jiangotto/Pomo/Assets/TestPatterns/epd_16_grayscale_1216x684.png

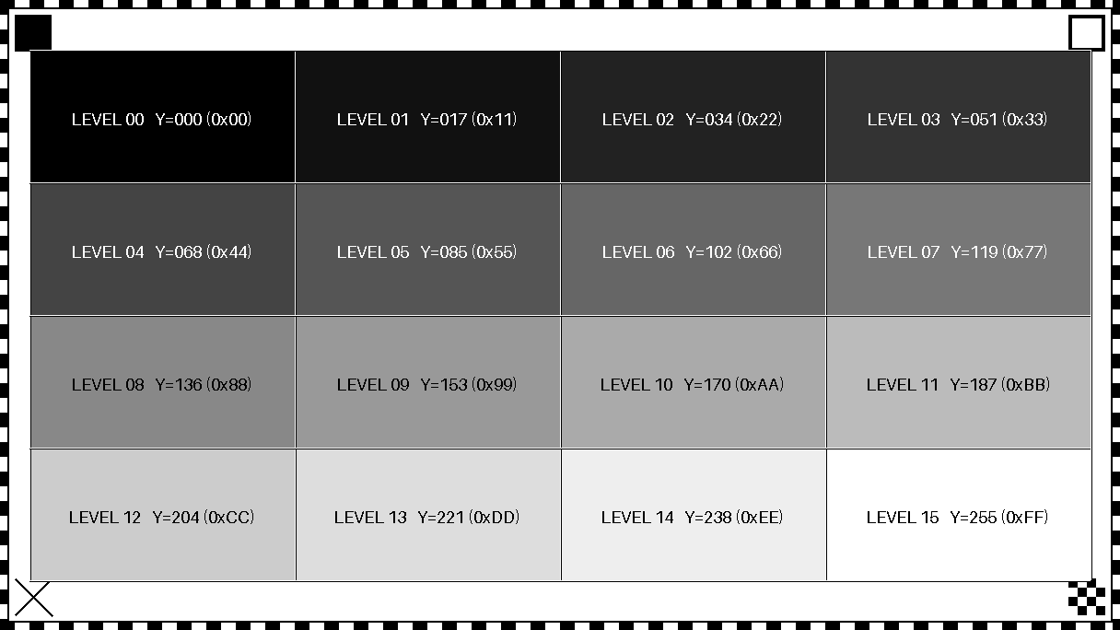
Assets/TestPatterns/epd_16_grayscale_1216x684.png
