jiangotto/Pomo/Firmware/V2/src/pomo.v

// Copyright Yuhan Jiang 2025-2026
//
// This source describes Open Hardware and is licensed under the CERN-OHL-S v2
//
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
`timescale 1ns/1ps
`include "defines.vh"

module pomo (
	input  wire         clk,
	input  wire         sys_ready,
	input  wire         rst,

	input  wire         vin_vsync,
	input  wire         vin_hsync,
	input  wire         vin_de,
	input  wire [3:0]   vin_pixel,
	input  wire         mode_cmd_valid,
	input  wire [3:0]   mode_cmd_value,
	input  wire         reinit_cmd_valid,

	output wire         bo_clk,
	output wire         bo_vsync,
	output wire         bo_de,
	output reg  [15:0]  bo_data,
	output wire         bi_clk,
	output wire         bi_vsync,
	output wire         bi_de,
	input  wire         bi_den,
	input  wire [15:0]  bi_data,
	output reg  [3:0]   active_mode,

	output wire         epd_gdclk,
	output wire         epd_gdsp,
	output wire         epd_sdclk,
	output wire         epd_sdle,
	output wire [15:0]  epd_data,
	output wire         epd_sdce
);
	// sys_ready combines PMIC state from sys_clk with HyperRAM calibration
	// state from the memory domain.  Synchronize the resulting stable level
	// before it controls any state in this pixel-clock domain.
	(* ASYNC_REG = "TRUE", syn_preserve = 1 *) reg [1:0] sys_ready_sync;
	always @(posedge clk) begin
		if (rst)
			sys_ready_sync <= 2'b00;
		else
			sys_ready_sync <= {sys_ready_sync[0], sys_ready};
	end
	wire sys_ready_clk = sys_ready_sync[1];

	// ============================================================
	// Scan Control
	//
	// Vertical:   counter-based. Frame line counts match defines.
	// Horizontal: signal-based. MIPI actual hsync/de timing may differ.
	// ============================================================

	// vertical timing (from defines, frame line counts are reliable)
	localparam [7:0]  VFP   = `DEFAULT_VFP;
	localparam [7:0]  VSYNC = `DEFAULT_VSYNC;
	localparam [7:0]  VBP   = `DEFAULT_VBP;
	localparam [11:0] VACT  = `EPD_VACT;

	// input edge detect
	reg vin_vsync_d;
	reg vin_hsync_d;

	always @(posedge clk) begin
		if (rst) begin
			vin_vsync_d <= 1'b0;
			vin_hsync_d <= 1'b0;
		end else begin
			vin_vsync_d <= vin_vsync;
			vin_hsync_d <= vin_hsync;
		end
	end

	wire vin_vsync_rise = vin_vsync & ~vin_vsync_d;
	wire vin_hsync_rise = vin_hsync & ~vin_hsync_d;

	// frame_valid: high from first hsync after vsync to last line of frame
	// vertical line counter
	reg        frame_valid;
	reg        frame_first_line;
	reg        vsync_just_hit;
	reg [10:0] scan_v_cnt;
	reg [5:0]  al_framecnt;

	always @(posedge clk) begin
		if (rst) begin
			frame_valid      <= 1'b0;
			frame_first_line <= 1'b0;
			vsync_just_hit   <= 1'b0;
			scan_v_cnt       <= 11'd0;
			al_framecnt      <= `LUT_FRAMES;
		end else if (!sys_ready_clk) begin
			frame_valid      <= 1'b0;
			frame_first_line <= 1'b0;
			vsync_just_hit   <= 1'b0;
			scan_v_cnt       <= 11'd0;
			al_framecnt      <= `LUT_FRAMES;
		end else begin
			vsync_just_hit <= vin_vsync_rise;

			if (vin_vsync_rise) begin
				frame_valid      <= 1'b0;
				frame_first_line <= 1'b1;
				scan_v_cnt       <= 11'd0;
				if (al_framecnt == 6'd0)
					al_framecnt <= `LUT_FRAMES;
				else
					al_framecnt <= al_framecnt - 6'd1;
			end else if ((frame_first_line && vin_hsync_rise) || (vsync_just_hit && vin_hsync)) begin
				frame_valid      <= sys_ready_clk;
				frame_first_line <= 1'b0;
				scan_v_cnt       <= 11'd0;
			end else if (frame_valid && vin_hsync_rise) begin
				frame_first_line <= 1'b0;
				if (scan_v_cnt == (VFP + VSYNC + VBP + VACT - 1'b1)) begin
					scan_v_cnt  <= 11'd0;
					frame_valid <= 1'b0;
				end else begin
					scan_v_cnt <= scan_v_cnt + 11'd1;
				end
			end else if (frame_valid) begin
				frame_first_line <= 1'b0;
			end else begin
				scan_v_cnt       <= 11'd0;
				frame_valid      <= 1'b0;
				frame_first_line <= 1'b0;
			end
		end
	end

	// scan region signals
	// vertical: counter-based
	// horizontal: signal-based (vin_hsync, vin_de)
	wire scan_in_vsync;
	wire scan_in_vbp;
	wire scan_in_vact;
	wire scan_in_vact_le;
	wire scan_in_gate_start;
	wire scan_in_gate_blank;
	wire scan_in_hsync;
	wire scan_in_hact;
	wire scan_in_act;

	assign scan_in_vsync = vin_vsync;
	assign scan_in_vbp   = frame_valid && (scan_v_cnt >= VSYNC) && (scan_v_cnt < VSYNC + VBP);
	assign scan_in_vact  = frame_valid && (scan_v_cnt >= VSYNC + VBP) && (scan_v_cnt < VSYNC + VBP + VACT);
	// Pomo streams a completed Source row into the panel one line before it is
	// latched.  Keep the established next-line window; Caster obtains the same
	// relationship from the phase of its own free-running scan counter.
	assign scan_in_vact_le = frame_valid &&
		(scan_v_cnt >= VSYNC + VBP + 1) &&
		(scan_v_cnt < VSYNC + VBP + VACT + 1);
	// Start STV early enough that the first active line supplies the final
	// internal shift before G1. Keep clocking through the trailing VFP so the
	// last Source row, latched there, receives the final Gate selection.
	localparam [10:0] GATE_START_LINE = VSYNC + VBP -
		(`EPD_STV_TO_G1_CKV - 1);
	assign scan_in_gate_start = frame_valid &&
		(scan_v_cnt == GATE_START_LINE);
	assign scan_in_gate_blank = frame_valid &&
		(scan_v_cnt >= GATE_START_LINE) && !scan_in_vact;
	assign scan_in_hsync = frame_valid && vin_hsync;
	assign scan_in_hact  = frame_valid && vin_de;
	assign scan_in_act   = scan_in_vact && scan_in_hact;

	reg after_hact;
	always @(posedge clk) begin
		if (rst)
			after_hact <= 1'b0;
		else if (vin_de)         
			after_hact <= 1'b1;  
		else if (vin_hsync)      
			after_hact <= 1'b0; 
	end
	wire scan_in_hbp = frame_valid && !vin_hsync && !vin_de && !after_hact;
	wire scan_in_hfp = frame_valid && !vin_hsync && !vin_de &&  after_hact;

	// ============================================================
	// Blue noise coordinates
	// ============================================================
	// Count the physical source coordinate at the reordered stream. The blue
	// noise ROM is 64x64, so both coordinates must retain six address bits.
	reg [5:0] noise_phys_x;

	always @(posedge clk) begin
		if (rst)
			noise_phys_x <= 6'd0;
		else if (vin_hsync_rise)
			noise_phys_x <= 6'd0;
		else if (vin_de)
			noise_phys_x <= noise_phys_x + 6'd1;
	end

	// Remove the vertical blanking offset before addressing the noise tile.
	// In reorder mode, convert the physical W x 2H scan coordinate back to
	// the original logical 2W x H coordinate so adjacent logical pixels use
	// adjacent entries of the blue-noise pattern:
	//   logical_x = 2*physical_x + physical_y[0]
	//   logical_y = physical_y / 2
	wire [10:0] noise_phys_y = scan_v_cnt - (VSYNC + VBP);
`ifdef EPD_PIXEL_REORDER
	wire [5:0] noise_x = {noise_phys_x[4:0], noise_phys_y[0]};
	wire [5:0] noise_y = noise_phys_y[6:1];
`else
	wire [5:0] noise_x = noise_phys_x;
	wire [5:0] noise_y = noise_phys_y[5:0];
`endif

	// ============================================================
	// Auto clear timer
	// ============================================================



	// ============================================================
	// Init state machine
	// ============================================================

	localparam INIT_IDLE     = 2'd0;
	localparam INIT_CLEARING = 2'd1;
	localparam INIT_NORMAL   = 2'd2;

	reg [1:0] init_state;
	reg [9:0] clear_frame_cnt;
	reg [3:0] requested_mode;

	function is_display_mode;
		input [3:0] mode;
		begin
			is_display_mode = (mode == 4'h8) || (mode == 4'hA) ||
			                  (mode == 4'hB) || (mode == 4'hC);
		end
	endfunction

	always @(posedge clk) begin
		if (rst) begin
			init_state      <= INIT_IDLE;
			clear_frame_cnt <= 10'd0;
			requested_mode  <= `EPD_DEFAULT_MODE;
			active_mode     <= `EPD_DEFAULT_MODE;
		end else begin
			if (mode_cmd_valid && is_display_mode(mode_cmd_value))
				requested_mode <= mode_cmd_value;

			if (!sys_ready_clk) begin
				// A PMIC power cycle always restarts the normal clear sequence.
				init_state      <= INIT_IDLE;
				clear_frame_cnt <= 10'd0;
			end else if (reinit_cmd_valid) begin
				// Preserve requested_mode, but restart the complete initialization
				// clear at the next clean input-frame boundary.
				init_state      <= INIT_IDLE;
				clear_frame_cnt <= 10'd0;
			end else case (init_state)
				INIT_IDLE: begin
					if (sys_ready_clk && vin_vsync_rise) begin
						active_mode <= requested_mode;
						init_state <= INIT_CLEARING;
					end
				end
				INIT_CLEARING: begin
					if (vin_vsync_rise) begin
						if (requested_mode != active_mode) begin
							active_mode <= requested_mode;
							clear_frame_cnt <= 10'd0;
						end else if (clear_frame_cnt == `CLEAR_FRAMES) begin
							init_state <= INIT_NORMAL;
							clear_frame_cnt <= 10'd0;
						end else begin
							clear_frame_cnt <= clear_frame_cnt + 10'd1;
						end
					end
				end
				INIT_NORMAL: begin
					if (vin_vsync_rise && (requested_mode != active_mode)) begin
						active_mode <= requested_mode;
						init_state <= INIT_CLEARING;
						clear_frame_cnt <= 10'd0;
					end
				end
			endcase
		end
	end

	wire [1:0] sys_mode;
	assign sys_mode = (init_state == INIT_CLEARING) ? `SYS_CLEAR : `SYS_NORMAL;

	// ============================================================
	// BI & BO
	// ============================================================

	assign bi_clk   = clk;
	assign bi_vsync = ~scan_in_vsync;
	assign bi_de    = scan_in_act;

	wire bi_vsync_dl;
	delay #(
		.DEPTH(6), 
		.WIDTH(1)
	) u_delay_bi_vsync (
		.clk(clk), 
		.rst(rst),
		.din(bi_vsync),
		.dout(bi_vsync_dl)
	);

	wire bi_de_dl;
	delay #(
		.DEPTH(6), 
		.WIDTH(1)
	) u_delay_bi_de (
		.clk(clk), 
		.rst(rst),
		.din(bi_de),
		.dout(bi_de_dl)
	);

	assign bo_clk   = clk;
	assign bo_vsync = bi_vsync_dl;
	assign bo_de    = bi_de_dl;

	// ============================================================
	// Stage 1 — 2-cycle delay, align vin_pixel with HyperRAM read
	// ============================================================

//  wire s1_active;
//  delay #(
//      .DEPTH(2), 
//      .WIDTH(1)
//  ) u_delay_s1_active (
//      .clk(clk), 
//      .rst(rst),
//      .din(bi_de),
//      .dout(s1_active)
//  );

	wire [3:0] s1_vin_pixel;
	delay #(
		.DEPTH(2), 
		.WIDTH(4)
	) u_delay_s1p (
		.clk(clk), 
		.rst(rst),
		.din(vin_pixel),
		.dout(s1_vin_pixel)
	);

	// ============================================================
	// Stage 2 — latch framebuffer read + aligned input pixel
	// ============================================================
	reg        s2_active;
	reg [15:0] s2_bi_pixel;
	reg [3:0]  s2_vin_pixel;

	always @(posedge clk) begin
		if (rst) begin
			s2_active <= 1'b0;
		end else begin
			s2_active <= bi_den;
			if (bi_den) begin
				s2_bi_pixel  <= bi_data;
				s2_vin_pixel <= s1_vin_pixel;
			end
		end
	end

		// ============================================================
		// Blue noise dithering
		// ============================================================
		wire [7:0] s2_vin_linear = {s2_vin_pixel, 4'b0};
		wire       s3_dith_1b;
		wire [3:0] s3_dith_4b;

		blue_noise_dithering u_dith (
			.clk     (clk),
			.rst     (rst),
			.vin     (s2_vin_linear),
			.vout_1b (s3_dith_1b),
			.vout_4b (s3_dith_4b),
			.x_pos   (noise_x),
			.y_pos   (noise_y)
		);

	// ============================================================
	// Stage 3 — LUT address generation & wvfmlut
	// ============================================================

	reg        s3_active;
	reg [15:0] s3_bi_pixel;
	reg [3:0]  s3_vin_pixel;

	always @(posedge clk) begin
		if (rst) begin
			s3_active <= 1'b0;
		end else begin
			s3_active    <= s2_active;
			s3_bi_pixel  <= s2_bi_pixel;
			s3_vin_pixel <= s2_vin_pixel;
		end
	end

	// Waveform lookup here
	// Waveform structure:
	// 14 bit address input
	//   6 bit sequence ID
	//   4 bit source grayscale
	//   4 bit destination grayscale
	// 2 bit data output
	// 32 Kb
	wire [13:0] ram_addr_rd;
	wire [1:0]  s4_lut_rd; // 1 cycle latency

	// See pixel_processing.v comments for more details
	// Only used for LUT modes.
	// Local counter (per pixel counter) is used for manual LUT modes
	// Global counter is used for auto LUT modes
	/*verilator lint_off UNUSEDSIGNAL */
	wire [15:0] wvfm_bi = s3_bi_pixel;
	/*verilator lint_on UNUSEDSIGNAL */
	wire use_local_counter =  wvfm_bi[15];
	wire [5:0] wvfm_fcnt_global_counter = wvfm_bi[9:4];
	wire [5:0] wvfm_fcnt_local_counter = al_framecnt;
	wire [5:0] wvfm_fcnt = use_local_counter ?
			wvfm_fcnt_local_counter : wvfm_fcnt_global_counter;
	wire [5:0] wvfm_fseq = `LUT_FRAMES - wvfm_fcnt;
	wire [3:0] wvfm_src_global_counter = wvfm_bi[13:10];
	wire [3:0] wvfm_src_local_counter = wvfm_bi[7:4];
	wire [3:0] wvfm_src = use_local_counter ?
			wvfm_src_local_counter : wvfm_src_global_counter;
	wire [3:0] wvfm_tgt = wvfm_bi[3:0];
	assign ram_addr_rd = {wvfm_fseq, wvfm_tgt, wvfm_src};

	wvfmlut u_wcfmlut (
		.clk    (clk),
		.rst    (rst),
		.en     (s3_active),
		.addr   (ram_addr_rd),
		.dout   (s4_lut_rd)
	);

	// ============================================================
	// Stage 4 — pixel_processing 
	// ============================================================

	reg        s4_active;
	reg [15:0] s4_bi_pixel;
	reg [3:0]  s4_vin_pixel;
	reg [3:0]  s4_proc_vin;

	// Select the dithered value before the Stage 4 register boundary.  The
	// original pixel is retained separately because Auto-LUT also needs the
	// undithered input.  This moves the mode/dither mux out of the long pixel
	// state-machine path without adding a pipeline cycle.
	wire [3:0] s3_pixel_mode = s3_bi_pixel[15:12];
	wire       s3_use_dither_1b = (s3_pixel_mode == 4'hA);
	wire       s3_use_dither_4b =
		(s3_bi_pixel[15:14] == 2'b01) || (s3_pixel_mode == 4'hD);
	wire [3:0] s3_proc_vin = s3_use_dither_1b ? {4{s3_dith_1b}} :
	                            s3_use_dither_4b ? s3_dith_4b : s3_vin_pixel;

	always @(posedge clk) begin
		if (rst) begin
			s4_active <= 1'b0;
			s4_proc_vin <= 4'd0;
		end else begin
			s4_active    <= s3_active;
			s4_bi_pixel  <= s3_bi_pixel;
			s4_vin_pixel <= s3_vin_pixel;
			s4_proc_vin  <= s3_proc_vin;
		end
	end

	wire [1:0]  pixel_comb;
	wire [15:0] bo_pixel_comb;

	wire [3:0] proc_pixel = s4_vin_pixel;
	wire [15:0] proc_bi = s4_bi_pixel;
	wire [15:0] proc_bo;
	wire [1:0] proc_lut_rd = s4_lut_rd;
	wire [1:0] proc_output;

	pixel_processing u_pixel_processing(
		.sys_mode(sys_mode),
		.active_mode(active_mode),
		.proc_pixel(proc_pixel),
		.proc_vin(s4_proc_vin),
		.proc_bi(proc_bi),
		.proc_bo(proc_bo),
		.proc_lut_rd(proc_lut_rd),
		.proc_output(proc_output),
		.al_framecnt(al_framecnt),
		.clear_frame_cnt(clear_frame_cnt)
	);

	// Output
	assign pixel_comb = frame_valid ? proc_output : 2'b00;
	assign bo_pixel_comb = frame_valid ? proc_bo : proc_bi;

	reg [1:0] current_pixel;
	always @(posedge clk) begin
		current_pixel <= (s4_active) ? pixel_comb : 2'b0;
		bo_data <= bo_pixel_comb;
	end

	// ============================================================
	// Caster Source/Gate output, adapted only for one pixel per clock
	// ============================================================
	// The existing Pomo path delays bi_de/bi_vsync by six clocks to align
	// framebuffer writeback with current_pixel. Apply that same established
	// structural latency to the scan regions; it is not a panel timing value.
	localparam [3:0] OUTPUT_PIPELINE_DELAY = 4'd6;
	wire [9:0] epd_scan_regions;
	delay #(
		.DEPTH(OUTPUT_PIPELINE_DELAY),
		.WIDTH(10)
	) u_delay_epd_scan_regions (
		.clk(clk),
		.rst(rst),
		.din({scan_in_gate_start, scan_in_gate_blank,
		      scan_in_vsync, scan_in_vbp, scan_in_vact,
		      scan_in_vact_le,
		      scan_in_hfp, scan_in_hsync, scan_in_hbp, scan_in_hact}),
		.dout(epd_scan_regions)
	);

	wire epd_vsync;
	wire epd_vbp;
	wire epd_vact;
	wire epd_vact_le;
	wire epd_gate_start;
	wire epd_gate_blank;
	wire epd_hfp;
	wire epd_hsync;
	wire epd_hbp;
	wire epd_hact;
	assign {epd_gate_start, epd_gate_blank,
	        epd_vsync, epd_vbp, epd_vact, epd_vact_le,
	        epd_hfp, epd_hsync, epd_hbp, epd_hact} = epd_scan_regions;
	wire epd_act = epd_vact && epd_hact;

	// Caster consumes four 2-bit pixels per core clock. Pomo consumes one,
	// therefore a half Source word is collected over a bus-width-derived number
	// of clocks. The rising/falling edge roles and blanking enables are unchanged.
	localparam integer SOURCE_HALF_BITS = `EPD_OUTPUT_WIDTH / 2;
	localparam integer SOURCE_HALF_PIXELS = `EPD_OUTPUT_WIDTH / 4;
	wire source_clk_en = epd_hfp || epd_hsync || epd_hact;
	reg [2:0] source_half_pixel_count;
	reg [SOURCE_HALF_BITS-1:0] source_half_shift;
	reg [SOURCE_HALF_BITS-1:0] source_last_half;
	reg [15:0] source_data;
	reg source_clk;
	reg source_sdce;
	wire [SOURCE_HALF_BITS-1:0] source_half_next =
		{source_half_shift[SOURCE_HALF_BITS-3:0], current_pixel};

	always @(posedge clk) begin
		if (rst) begin
			source_half_pixel_count <= 3'd0;
			source_half_shift <= {SOURCE_HALF_BITS{1'b0}};
			source_last_half <= {SOURCE_HALF_BITS{1'b0}};
			source_data <= 16'd0;
			source_clk <= 1'b0;
			source_sdce <= 1'b1;
		end else if (!source_clk_en) begin
			// Caster forces SDCLK low during HBP to establish line phase.
			source_half_pixel_count <= 3'd0;
			source_half_shift <= {SOURCE_HALF_BITS{1'b0}};
			source_last_half <= {SOURCE_HALF_BITS{1'b0}};
			source_clk <= 1'b0;
			source_sdce <= 1'b1;
		end else begin
			source_half_shift <= source_half_next;
			if (source_half_pixel_count == SOURCE_HALF_PIXELS - 1) begin
				source_half_pixel_count <= 3'd0;
				source_clk <= ~source_clk;
				if (source_clk) begin
					// Falling edge: publish a complete word. The following
					// rising edge is the Source-driver sampling edge.
					source_data <=
						{{(16-`EPD_OUTPUT_WIDTH){1'b0}},
						 source_last_half, source_half_next};
					source_sdce <= !epd_act;
				end else begin
					source_last_half <= source_half_next;
				end
			end else begin
				source_half_pixel_count <= source_half_pixel_count + 3'd1;
			end
		end
	end

	assign epd_sdclk = source_clk;
	assign epd_sdce = source_sdce;
	assign epd_data = source_data;

	// Match Caster's Gate phase: CKV is high through HSYNC/HBP/HACT and falls
	// when HACT enters HFP.  SDLE is asserted at the following HSYNC, so Source
	// data is latched after the Gate falling edge instead of on that same edge.
	// Vertical blanking has no DE from which to recover HACT/HFP. Reproduce the
	// same leading high phase there from the real HSYNC plus the configured video
	// HBP, then leave CKV low for the rest of the row. This covers both the STV
	// lead-in and the trailing VFP clock which selects the final Gate row.
	reg [7:0] epd_gate_hbp_count;
	always @(posedge clk) begin
		if (rst || epd_hsync || !epd_gate_blank)
			epd_gate_hbp_count <= 8'd0;
		else if (epd_gate_hbp_count < `DEFAULT_HBP)
			epd_gate_hbp_count <= epd_gate_hbp_count + 8'd1;
	end
	wire epd_gate_blank_high = epd_gate_blank &&
		(epd_hsync || (epd_gate_hbp_count < `DEFAULT_HBP));
	wire epd_gate_active_high = epd_vact &&
		(epd_hsync || epd_hbp || epd_hact);
	wire epd_gdclk_pre = epd_gate_blank_high || epd_gate_active_high;
	reg epd_gdclk_delay;
	always @(posedge clk) begin
		if (rst)
			epd_gdclk_delay <= 1'b0;
		else
			epd_gdclk_delay <= epd_gdclk_pre;
	end

	assign epd_gdclk = epd_gdclk_delay;
	assign epd_gdsp = epd_gate_start ? 1'b0 : 1'b1;
	assign epd_sdle = epd_hsync && epd_vact_le;

endmodule
